luwangg/OzLockConBadge2017/hardware/OzLockCon.bmp

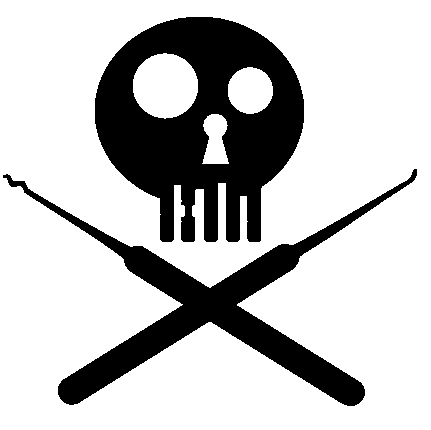
hardware/OzLockCon.bmp
