luwangg/OzLockConBadge2017/hardware/Panelization/Test_Combined_Bottom.png

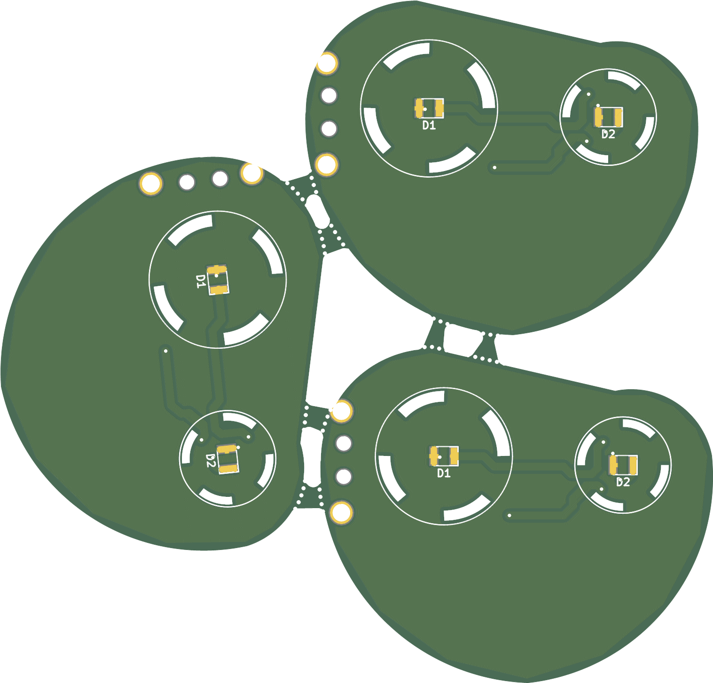
hardware/Panelization/Test_Combined_Bottom.png
