luwangg/OzLockConBadge2017/hardware/Verification/bcu.png

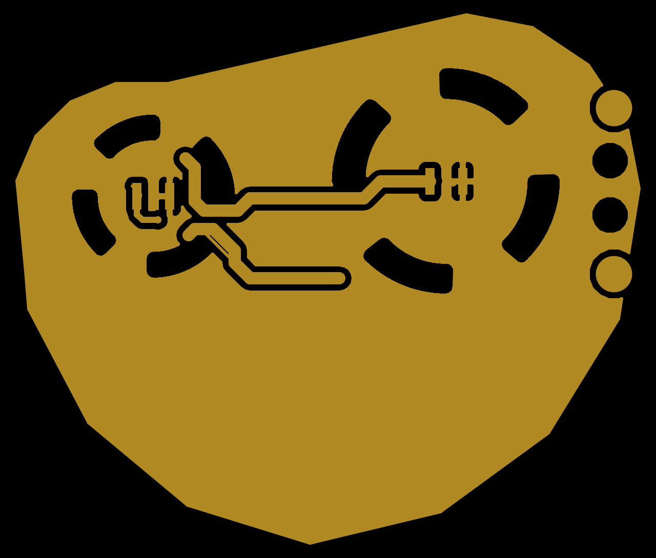
hardware/Verification/bcu.png
