luwangg/OzLockConBadge2017/hardware/Verification/bmask.png

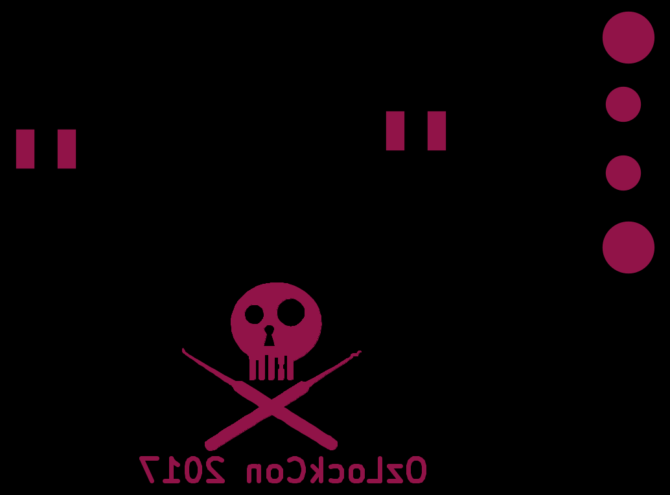
hardware/Verification/bmask.png
