luwangg/OzLockConBadge2017/hardware/Verification/bsilk.png

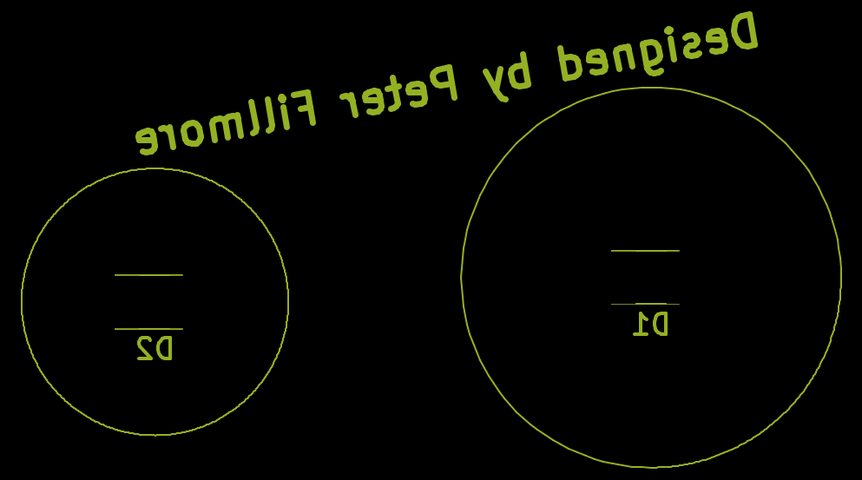
hardware/Verification/bsilk.png
