luwangg/OzLockConBadge2017/hardware/Verification/drill.png

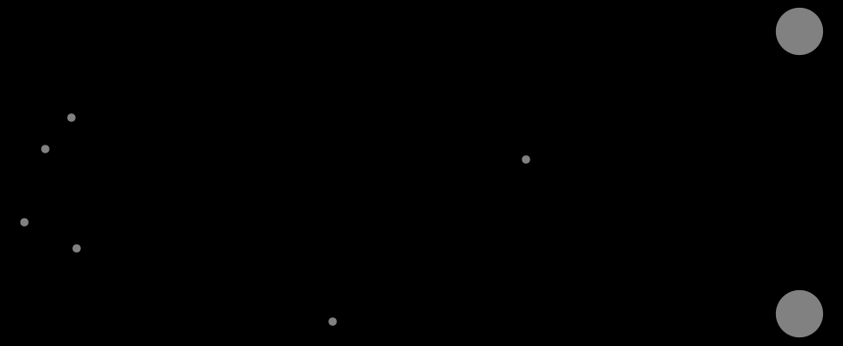
hardware/Verification/drill.png
