luwangg/OzLockConBadge2017/hardware/Verification/fcu.png

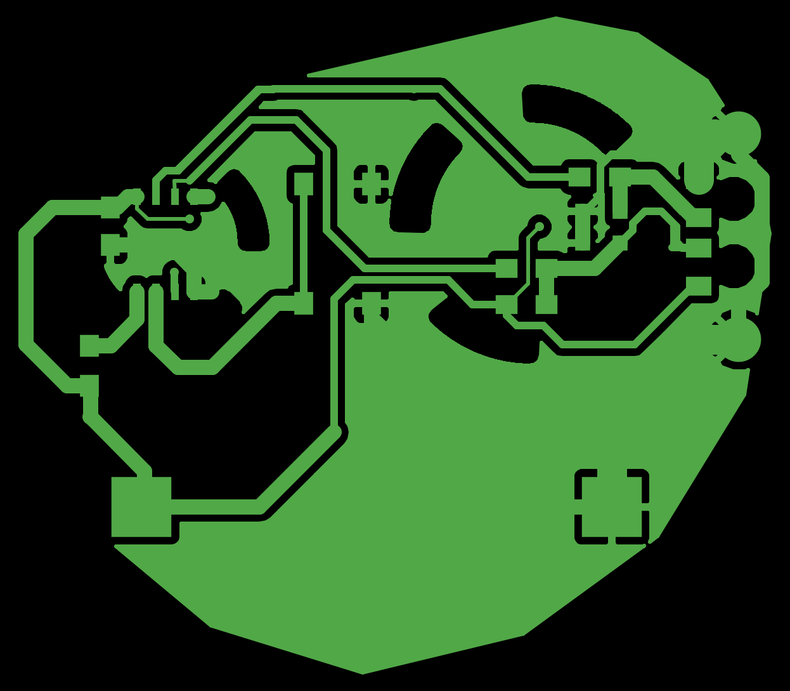
hardware/Verification/fcu.png
