luwangg/OzLockConBadge2017/hardware/Verification/fmask.png

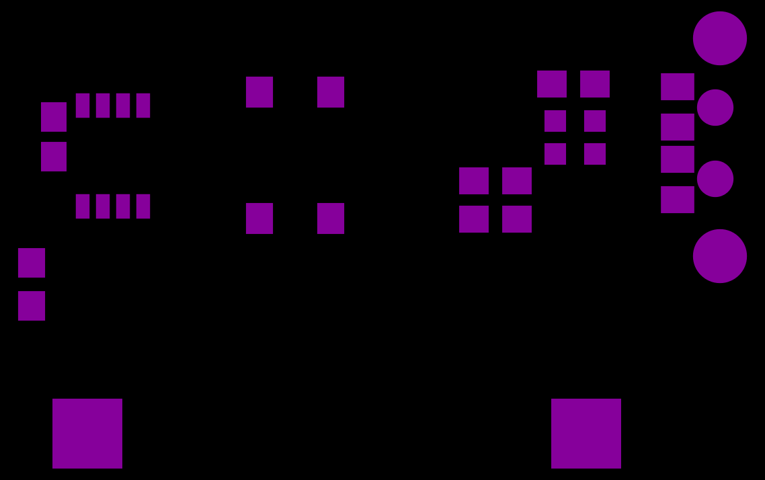
hardware/Verification/fmask.png
