luwangg/OzLockConBadge2017/hardware/Verification/fsilk.png

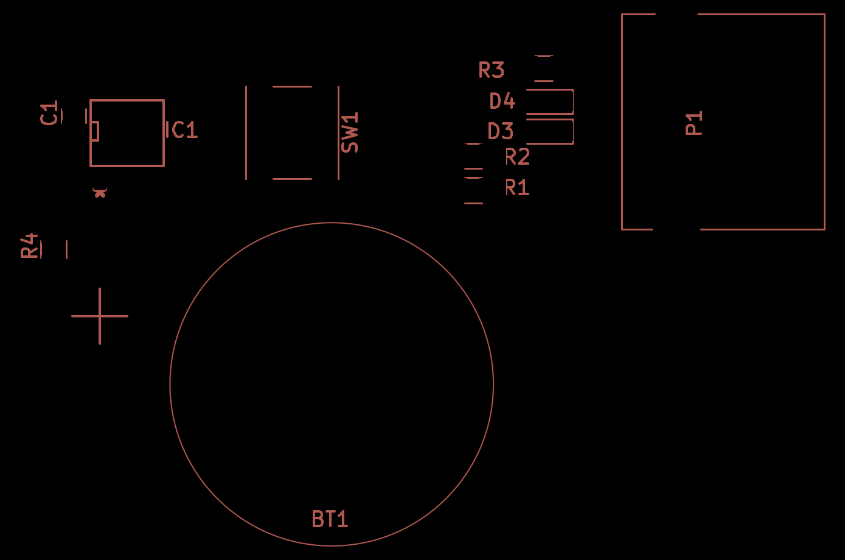
hardware/Verification/fsilk.png
